sidram1705/Munch_challenge/Munch_stepper_motor.kicad_sch

## KiCad design Munch_stepper_motor.kicad_sch (2025-09-18)

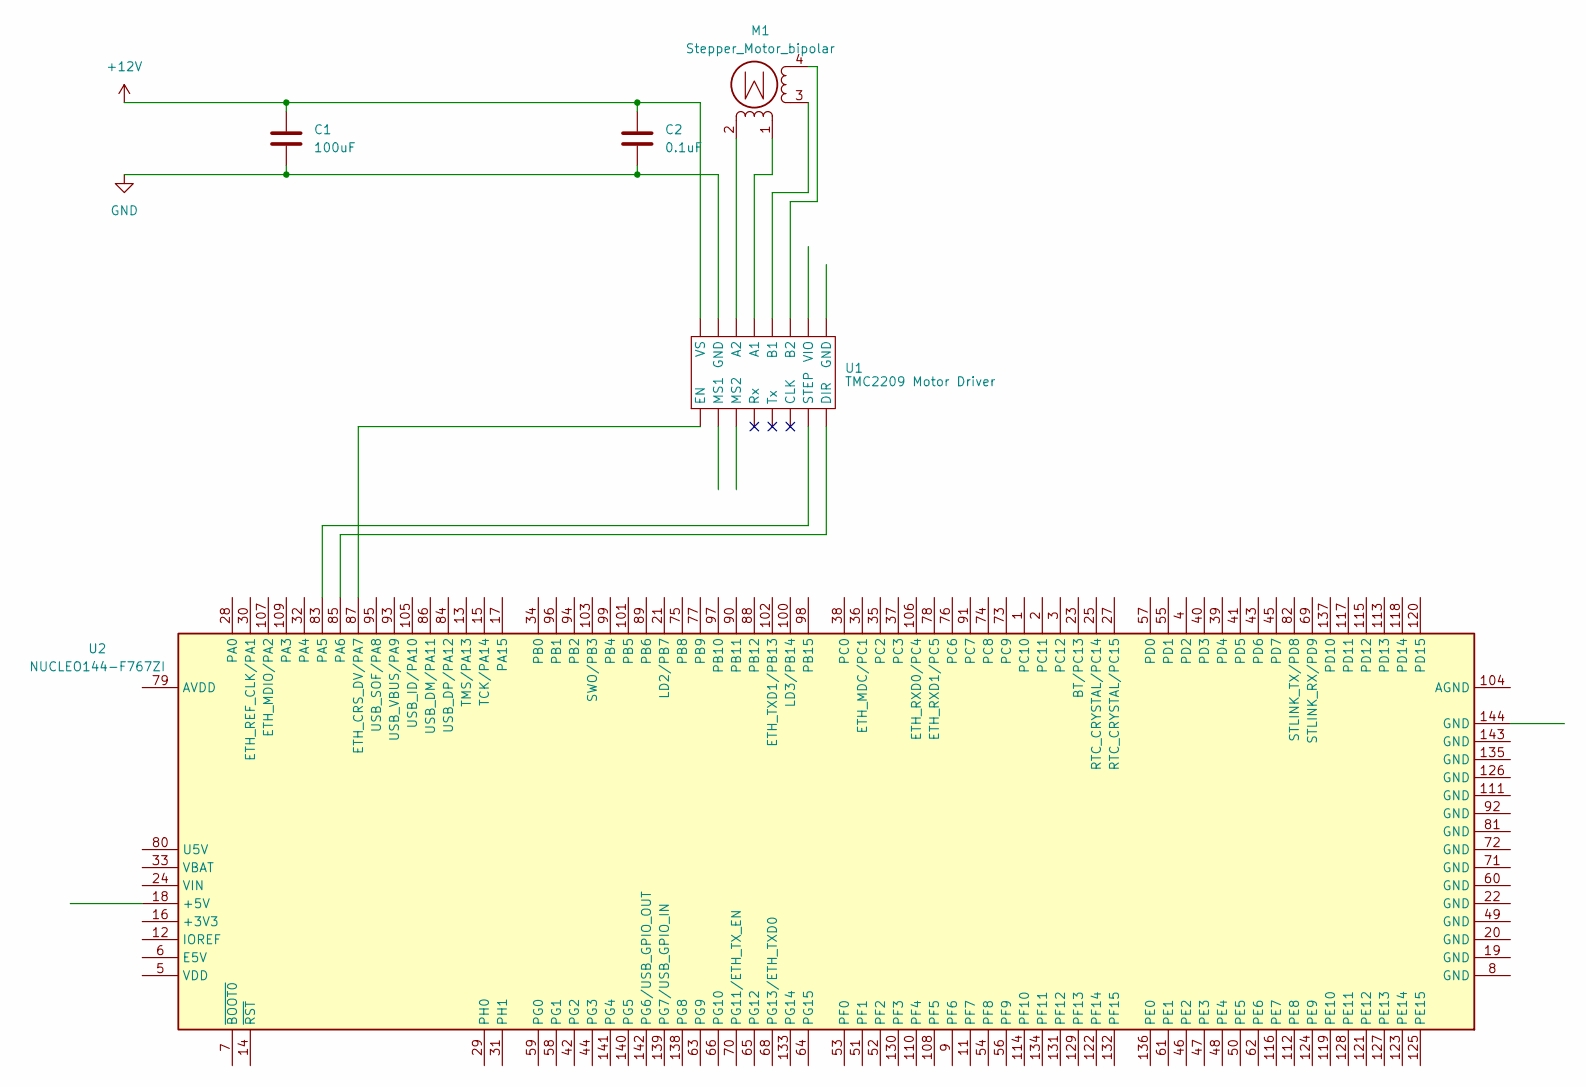
[picture p4: schematic Munch_stepper_motor.kicad_sch]

Parts:
C1: 100uF
C2: 0.1uF
M1: Stepper_Motor_bipolar
U1: TMC2209 Motor Driver
U2: NUCLEO144-F767ZI; ST_Morpho_Connector_144_STLink

Connections:
+12V: C1.1, C2.1, U1.
GND: C1.2, C2.2, U1.
unnamed: M1.1, U1.
unnamed: M1.2 (-), U1.
unnamed: M1.3, U1.
unnamed: M1.4, U1.
unnamed: U1., U2.83 (PA5), U2.85 (PA6), U2.87 (ETH_CRS_DV/PA7)
